KG-e/500W-MRF300-automatic-amplifier/LPF/14meg_lpf1.asc

C1: cap; 280p
C2: cap; 10p
C3: cap; 435p
C4: cap; 30p
C5: cap; 260p
L1: ind; 0.68u
L2: ind; 0.63u
R1: res; 50R
V1: voltage; ""; AC 1; Rser=50
Named nets: 0
.ac dec 101 1Meg 120Meg
14meg LPF (14-14.5)
(V(n003)*I(R1))/(V(n001)*I(V1))
V(n001)/I(V1)
