KG-e/500W-MRF300-automatic-amplifier/LPF/21meg_lpf1.asc

C1: cap; 165p
C2: cap; 15p
C3: cap; 265p
C4: cap; 35p
C5: cap; 145p
L1: ind; 0.45u
L2: ind; 0.38u
R1: res; 50R
V1: voltage; ""; AC 1; Rser=50
Named nets: 0
.ac dec 101 1Meg 120Meg
21meg LPF (21.1-21.5)
(V(n003)*I(R1))/(V(n001)*I(V1))
V(n001)/I(V1)
;.ac dec 101 21.1Meg 21.5Meg
