KG-e/500W-MRF300-automatic-amplifier/LPF/28meg_lpf1.asc

C1: cap; 125p
C2: cap; 10p
C3: cap; 210p
C4: cap; 15p
C5: cap; 120p
L1: ind; 0.33u
L2: ind; 0.32u
R1: res; 50R
V1: voltage; ""; AC 1; Rser=50
Named nets: 0
.ac dec 101 20Meg 120Meg
28meg LPF (26.9-29.2)
(V(n003)*I(R1))/(V(n001)*I(V1))
V(n001)/I(V1)
