KG-e/500W-MRF300-automatic-amplifier/LPF/3_5meg_lpf3.asc

C1: cap; 1.1n
C2: cap; 25p
C3: cap; 1.7n
C4: cap; 60p
C5: cap; 0.9n
L1: ind; 2.5u
L2: ind; 2.55u
R1: res; 50R
V1: voltage; ""; AC 1; Rser=50
Named nets: 0
.ac dec 101 1Meg 120Meg
3.5meg LPF (3.6-3.85)
(V(n003)*I(R1))/(V(n001)*I(V1))
razpon vhodne impedance ni hud
V(n001)/I(V1)
