KG-e/500W-MRF300-automatic-amplifier/LPF/7meg_lpf1.asc

C1: cap; 545p
C2: cap; 30p
C3: cap; 845p
C4: cap; 75p
C5: cap; 505p
L1: ind; 1.35u
L2: ind; 1.25u
R1: res; 50R
V1: voltage; ""; AC 1; Rser=50
Named nets: 0
.ac dec 101 1Meg 120Meg
7meg LPF (7-7.4)
(V(n003)*I(R1))/(V(n001)*I(V1))
V(n001)/I(V1)
